takashicompany/radialex/images/04.jpg

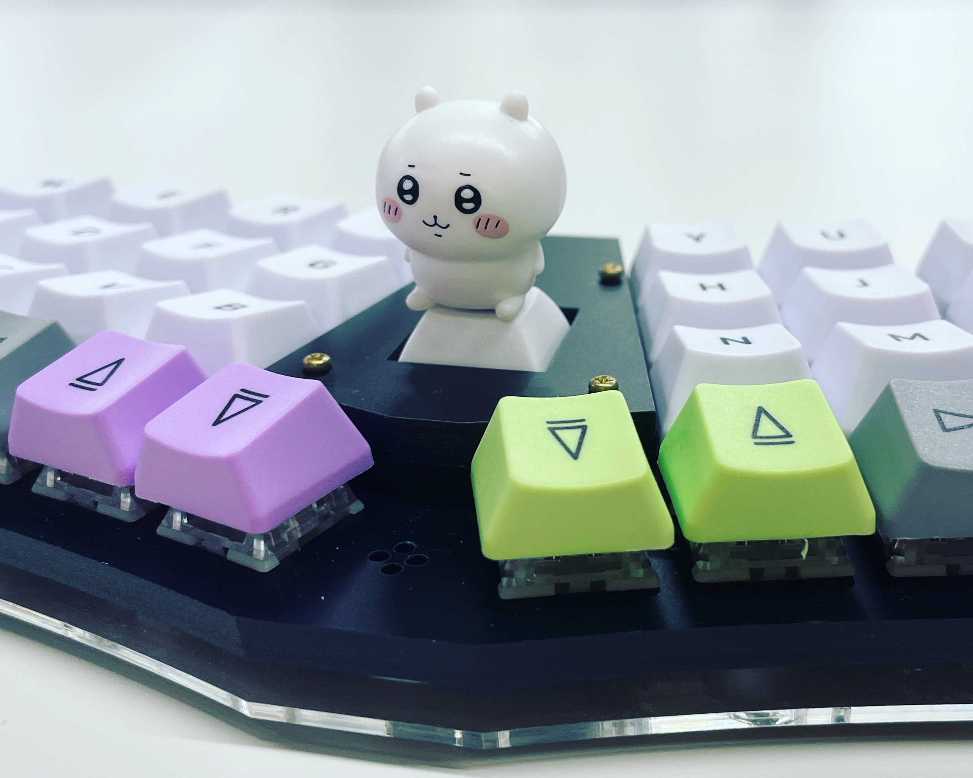
images/04.jpg
