takashicompany/radialex/images/06.jpg

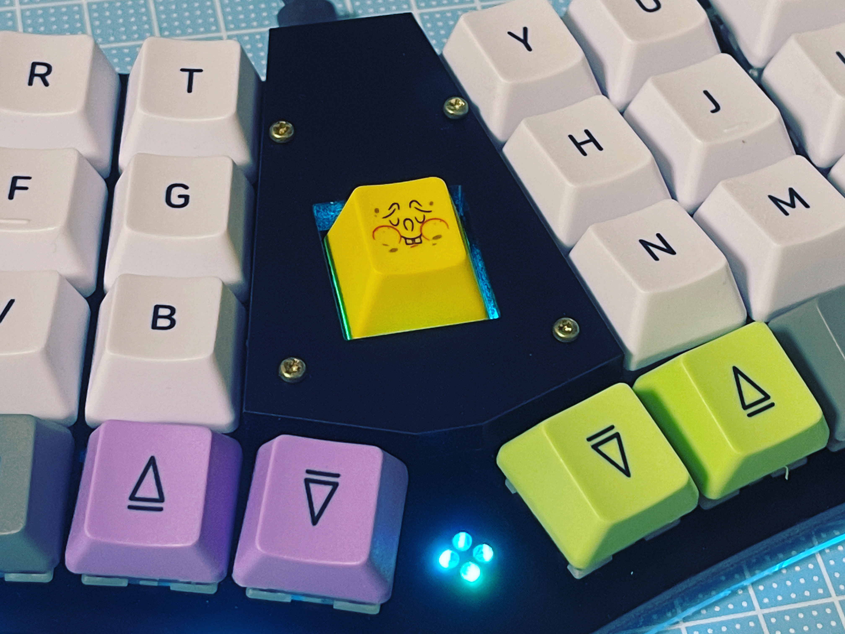
images/06.jpg
