takashicompany/radialex/images/07.jpg

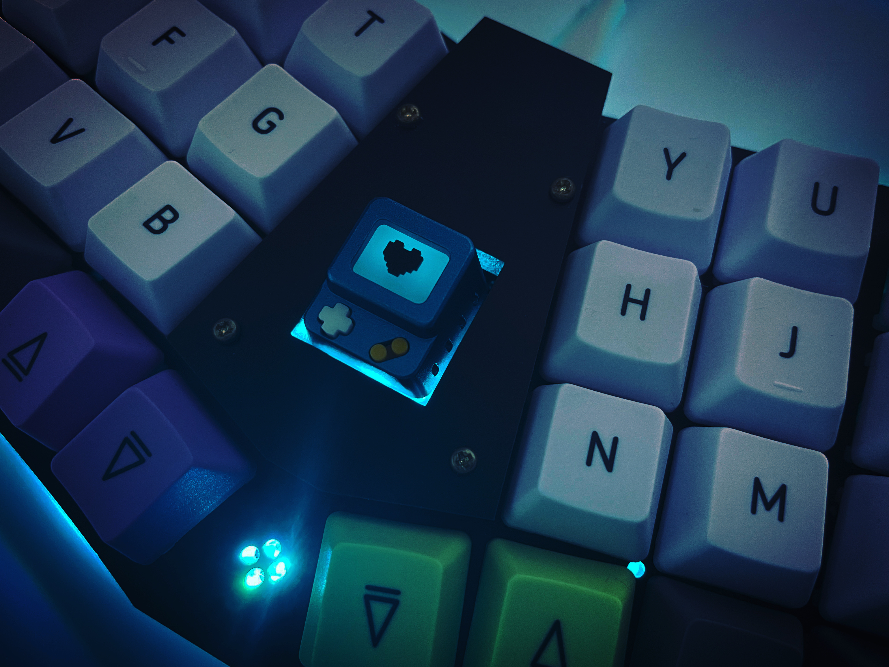
images/07.jpg
