takashicompany/radialex/images/08.jpg

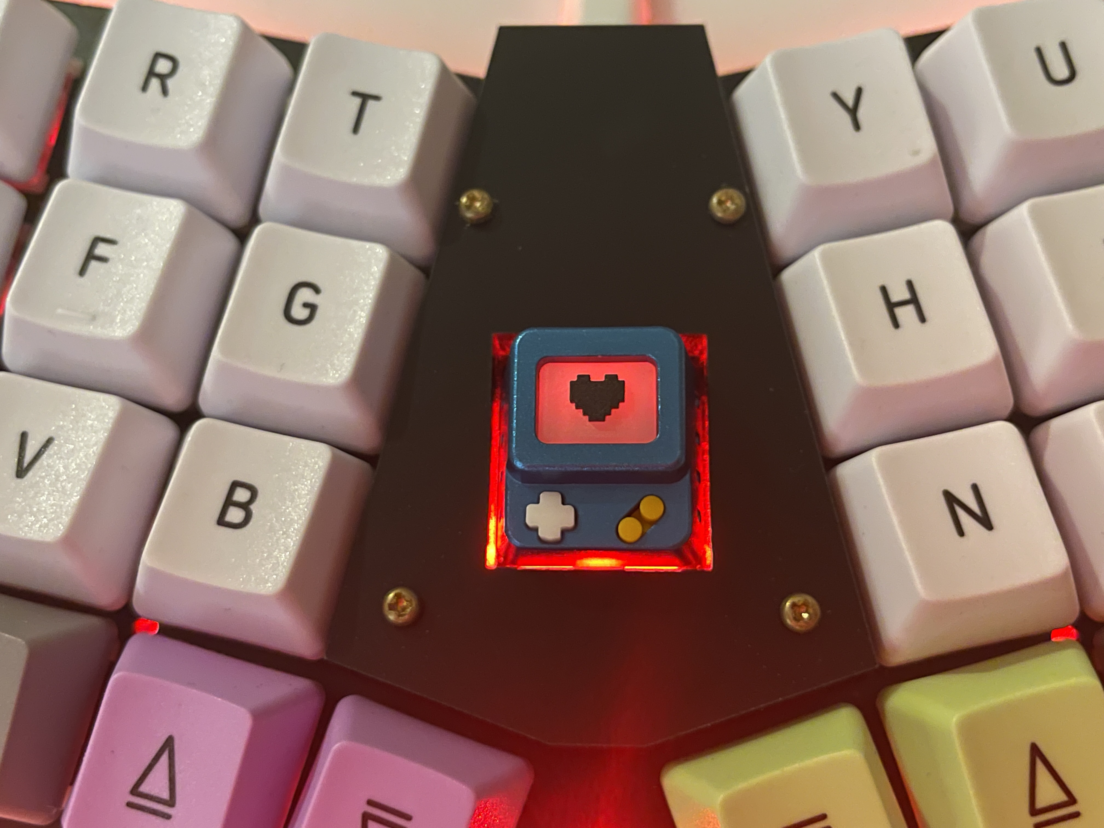
images/08.jpg
