takashicompany/radialex/images/09.jpg

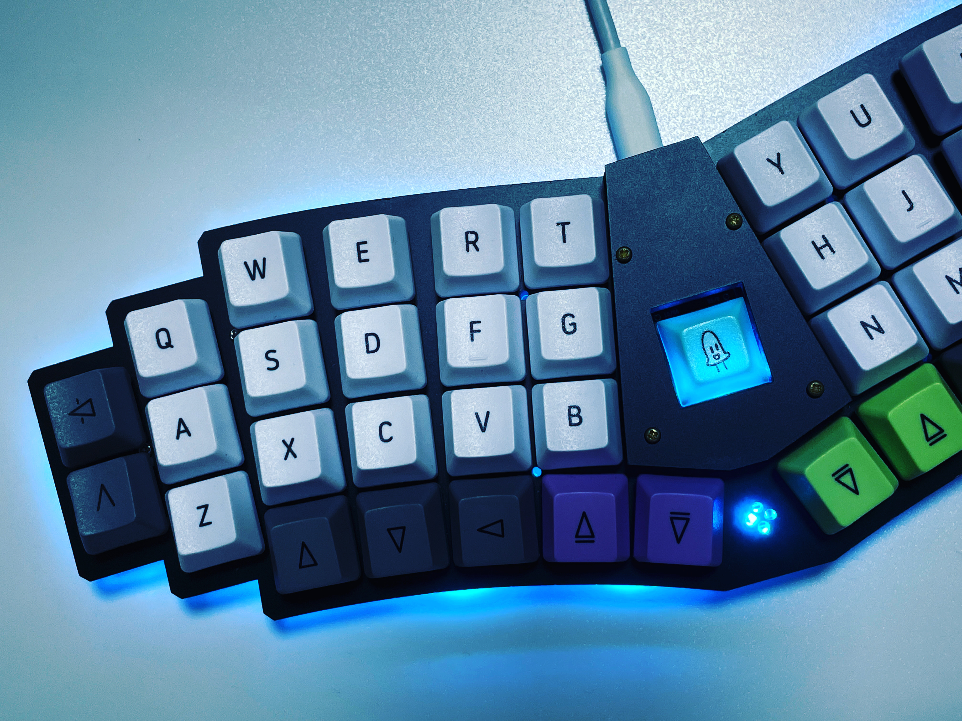
images/09.jpg
