takashicompany/radialex/images/10.jpg

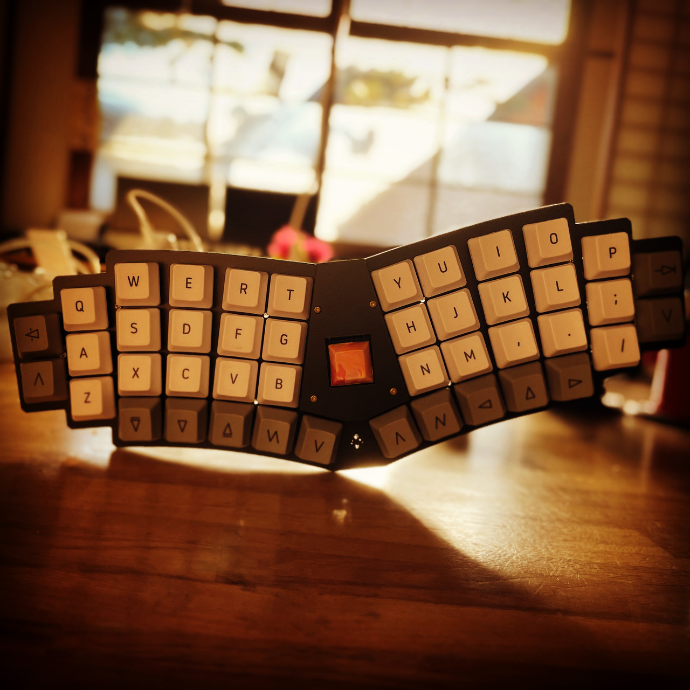
images/10.jpg
