takashicompany/radialex/images/12.jpg

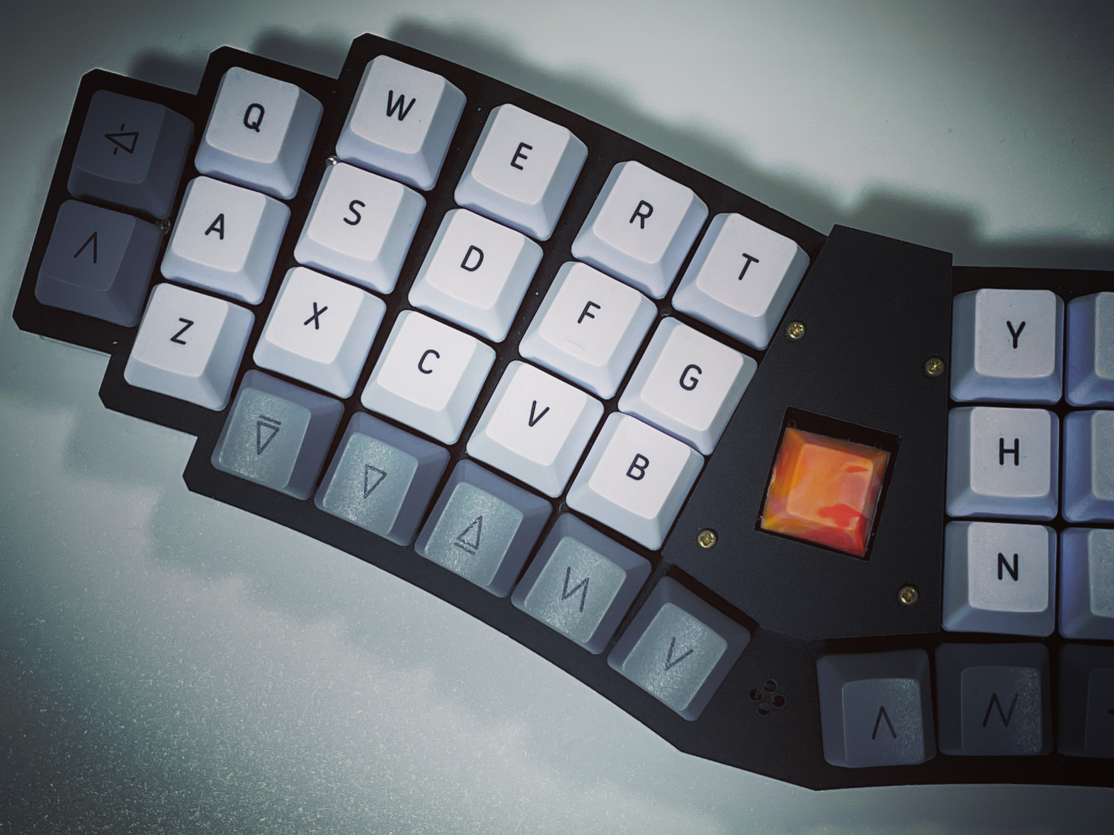
images/12.jpg
