takashicompany/radialex/images/13.jpg

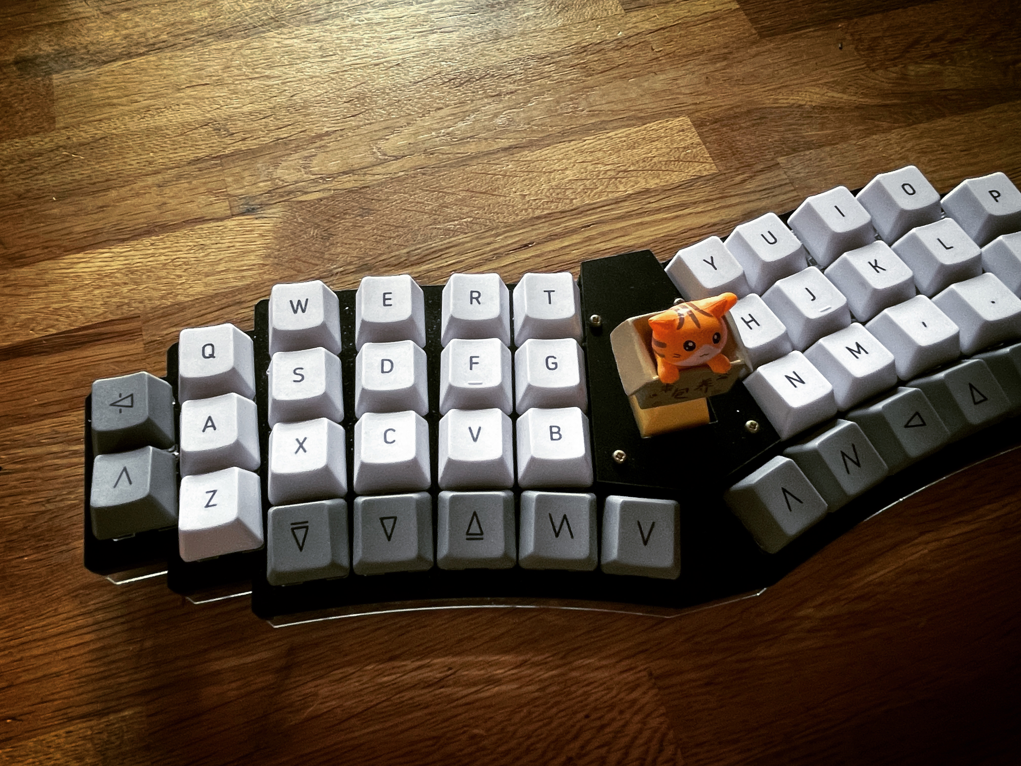
images/13.jpg
