takashicompany/radialex/images/22.jpg

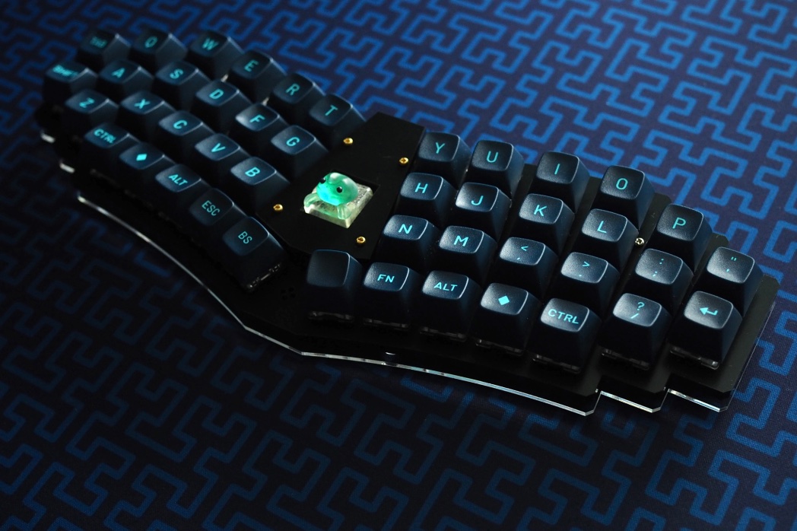
images/22.jpg
