takashicompany/radialex/images/24.jpg

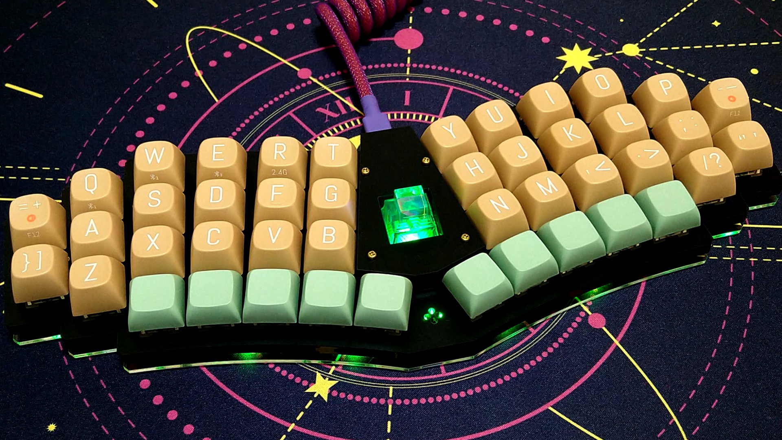
images/24.jpg
