takashicompany/radialex/images/qmk.jpg

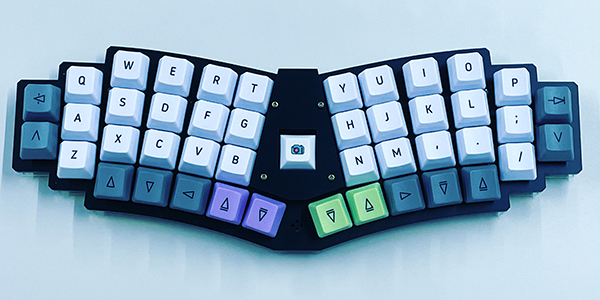
images/qmk.jpg
