takashicompany/radialex/images/build/IMG_8009.jpg

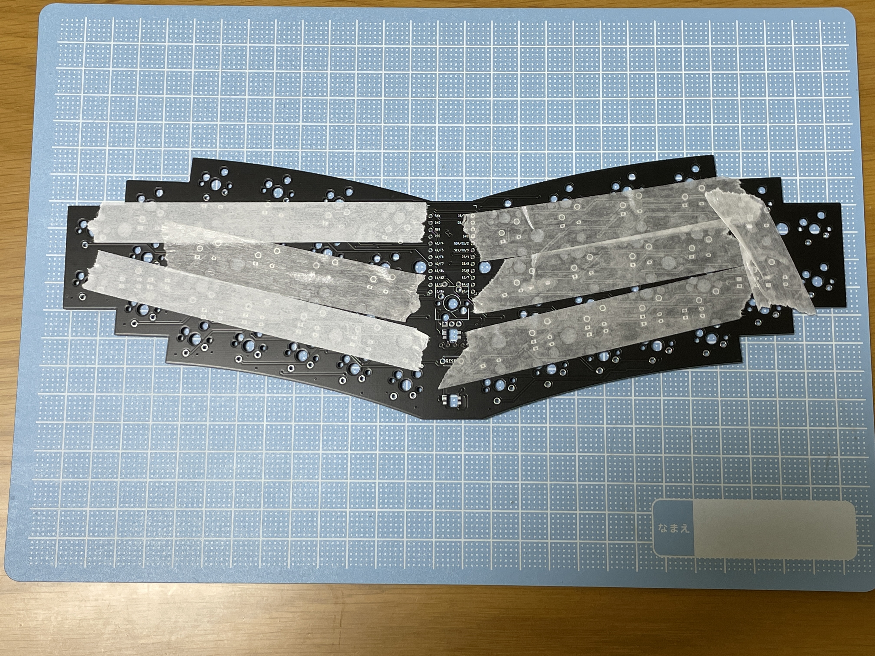
images/build/IMG_8009.jpg
