takashicompany/radialex/images/build/IMG_8306.jpg

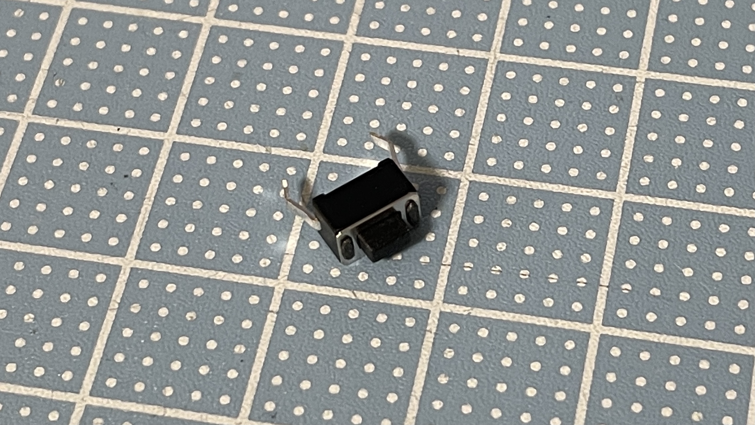
images/build/IMG_8306.jpg
