takashicompany/radialex/images/build/IMG_8320.jpg

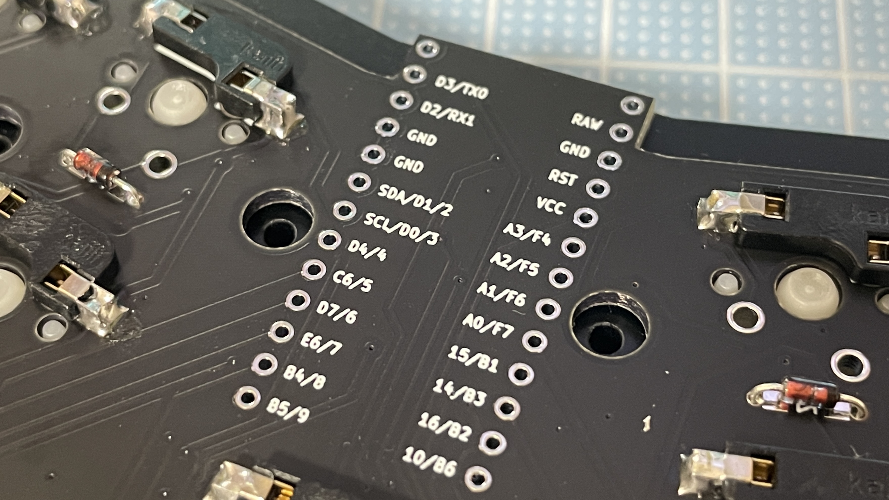
images/build/IMG_8320.jpg
