takashicompany/radialex/images/build/IMG_8321.jpg

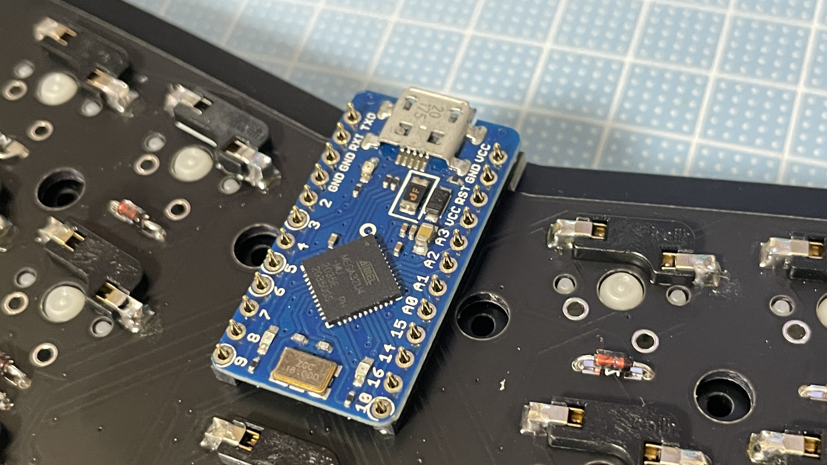
images/build/IMG_8321.jpg
