takashicompany/radialex/images/build/IMG_8509.jpg

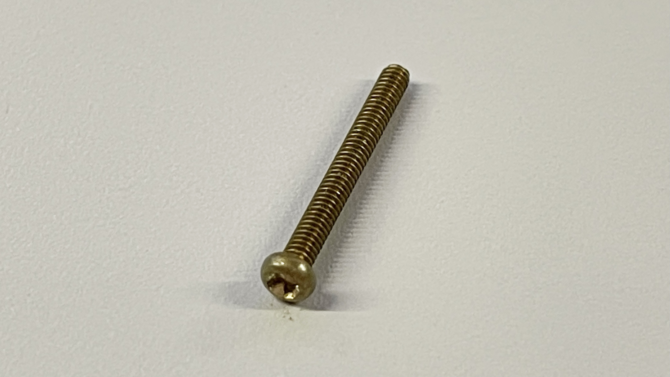
images/build/IMG_8509.jpg
