takashicompany/radialex/images/build/IMG_8510.jpg

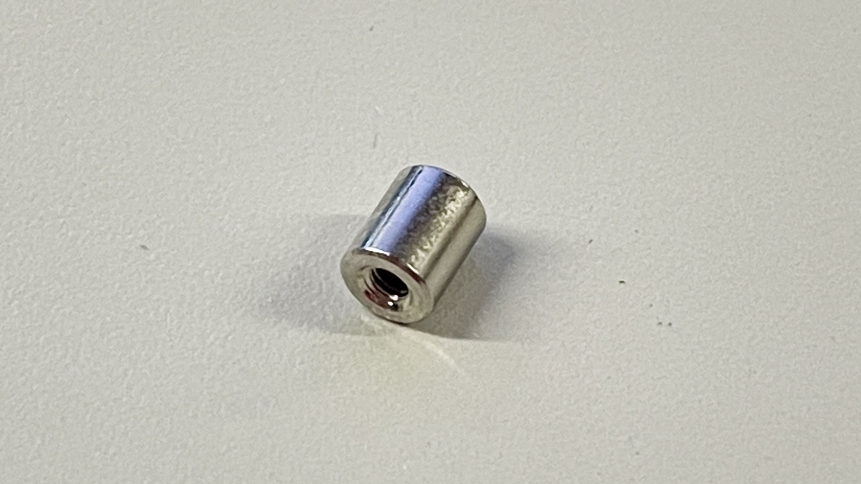
images/build/IMG_8510.jpg
