takashicompany/radialex/images/build/IMG_8511.jpg

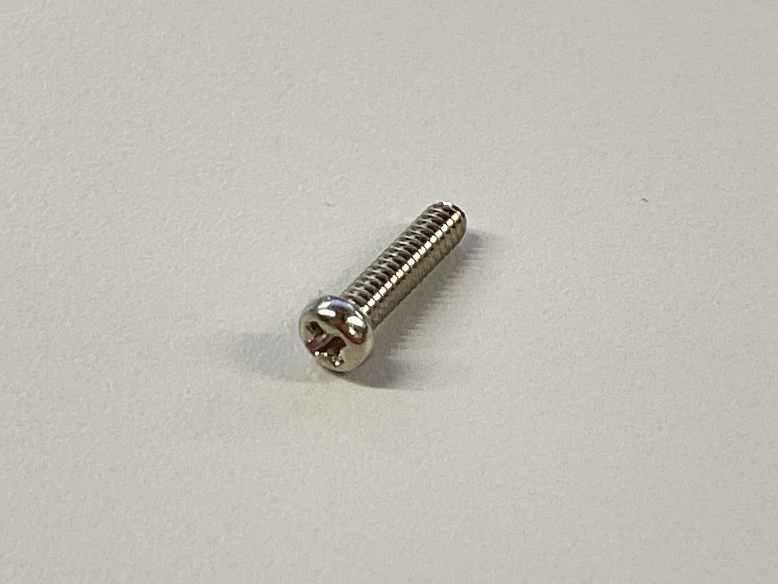
images/build/IMG_8511.jpg
