takashicompany/radialex/images/build/IMG_8513.jpg

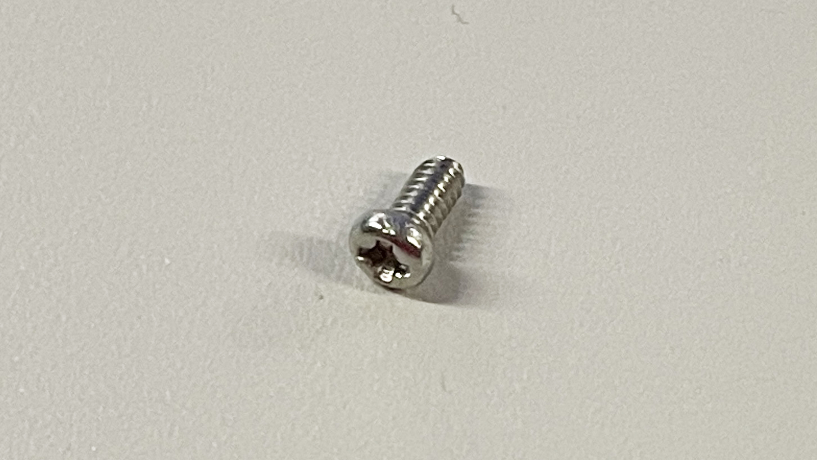
images/build/IMG_8513.jpg
