takashicompany/radialex/images/build/IMG_8516.jpg

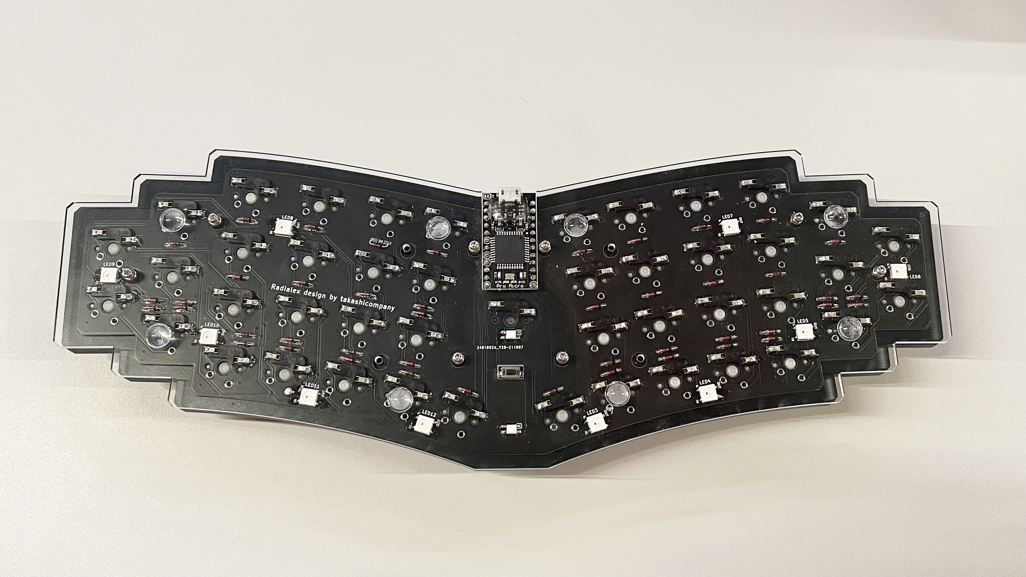
images/build/IMG_8516.jpg
