takashicompany/radialex/images/build/IMG_8812.jpg

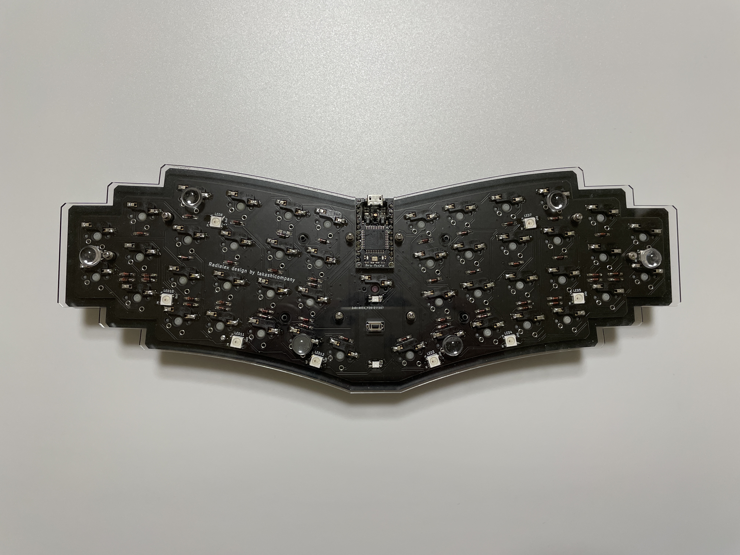
images/build/IMG_8812.jpg
