takashicompany/radialex/images/build/IMG_8814.jpg

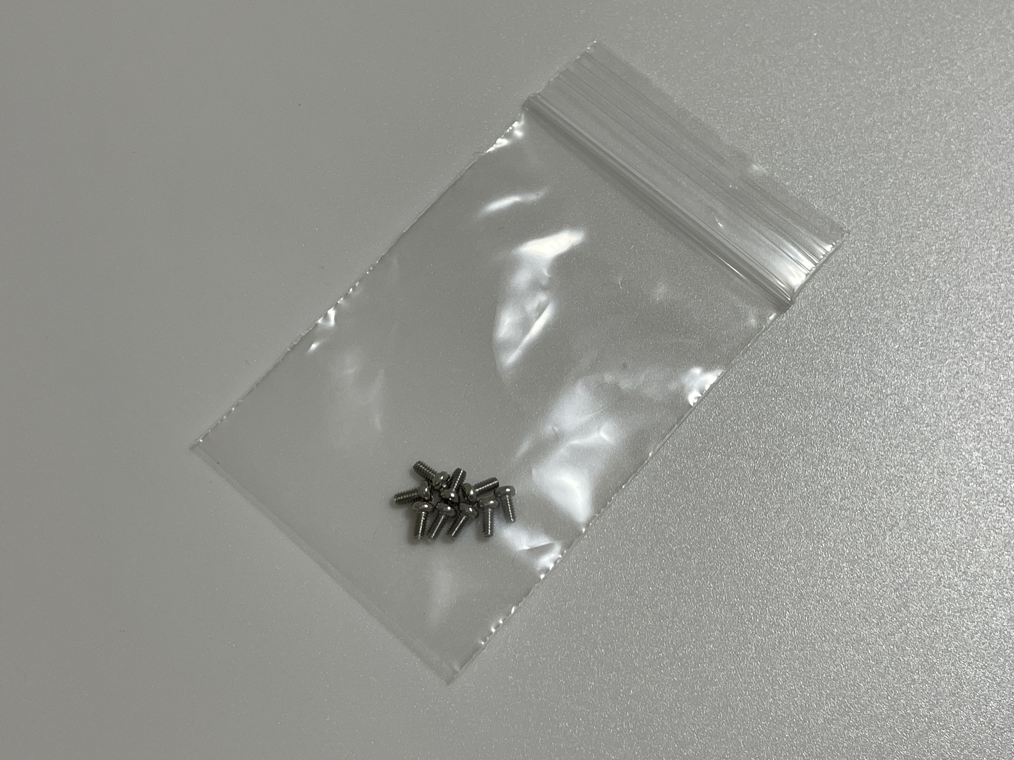
images/build/IMG_8814.jpg
