takashicompany/radialex/images/build/IMG_8815.jpg

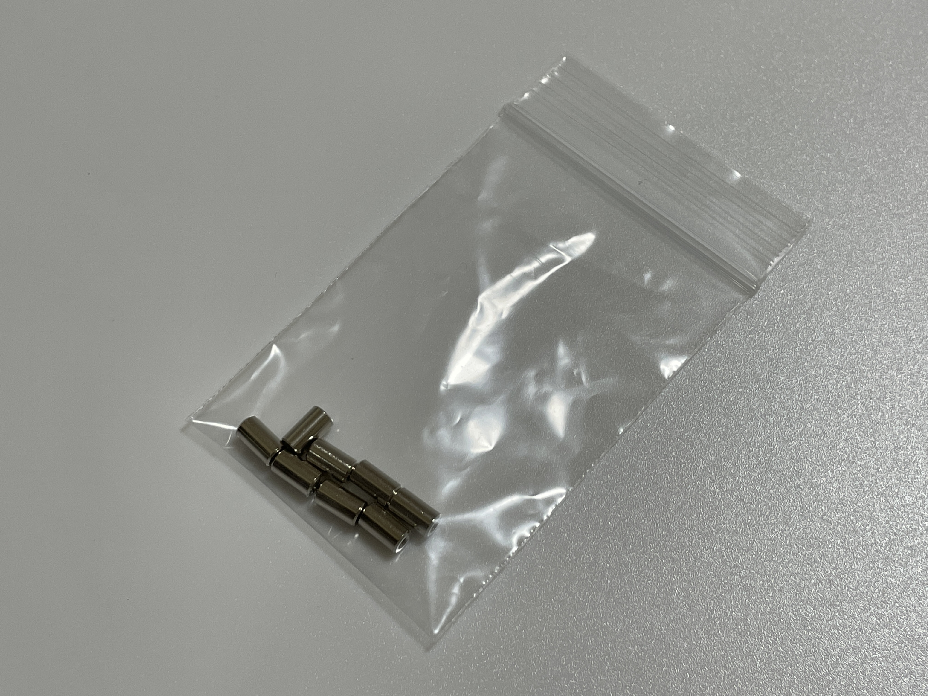
images/build/IMG_8815.jpg
