takashicompany/radialex/images/build/IMG_8816.jpg

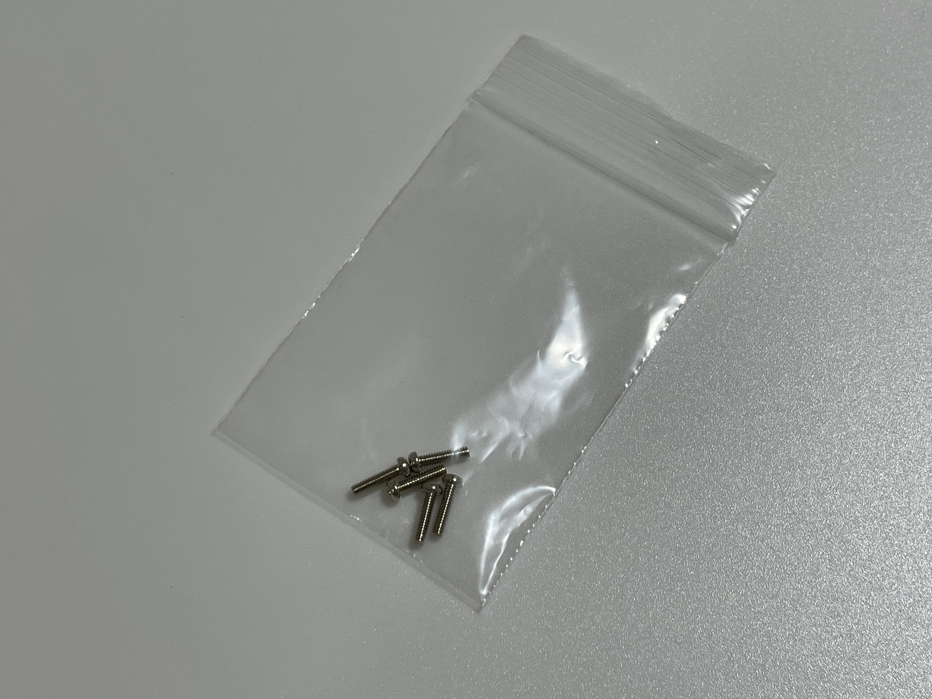
images/build/IMG_8816.jpg
