takashicompany/radialex/images/build/IMG_8817.jpg

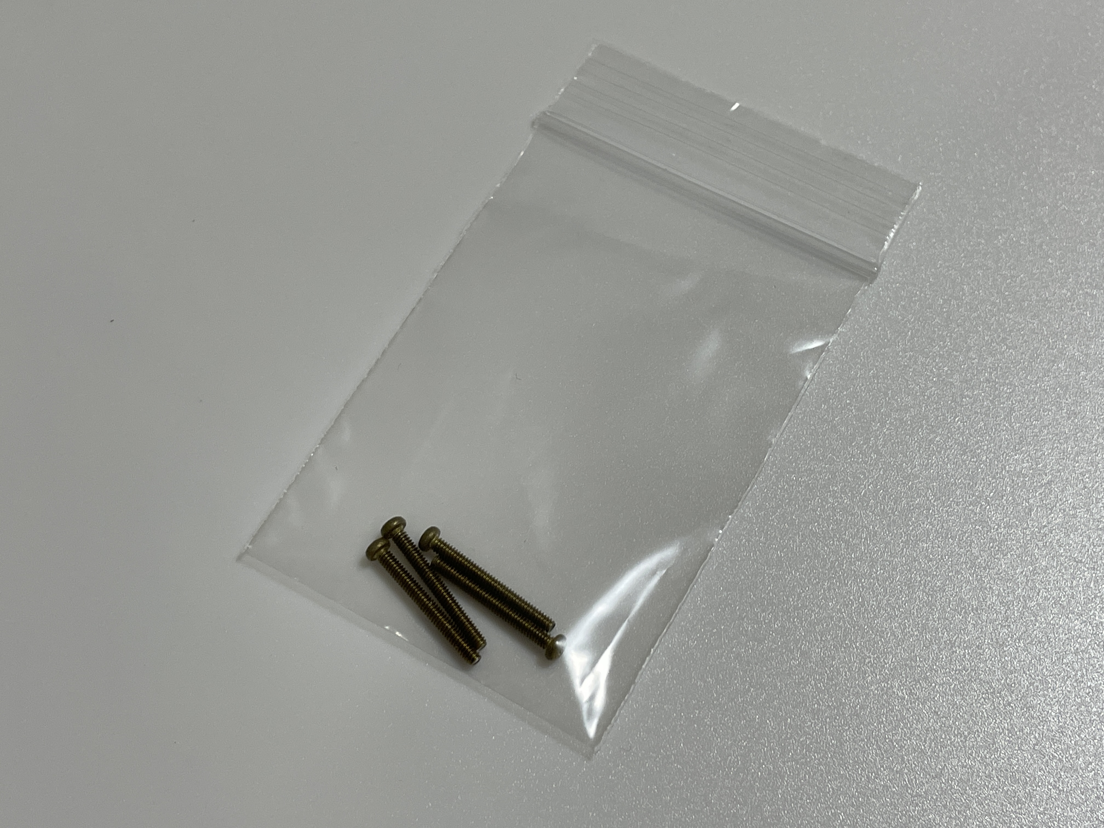
images/build/IMG_8817.jpg
