takashicompany/radialex/images/build/IMG_9180.jpg

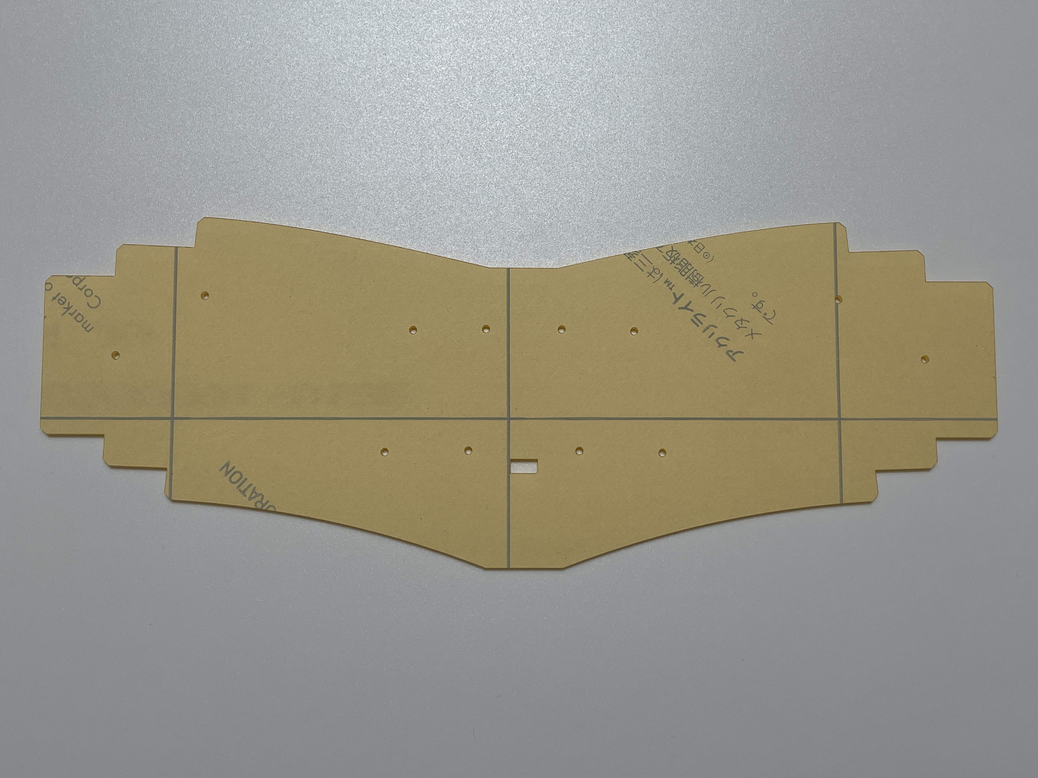
images/build/IMG_9180.jpg
