takashicompany/radialex/images/build/IMG_9181.jpg

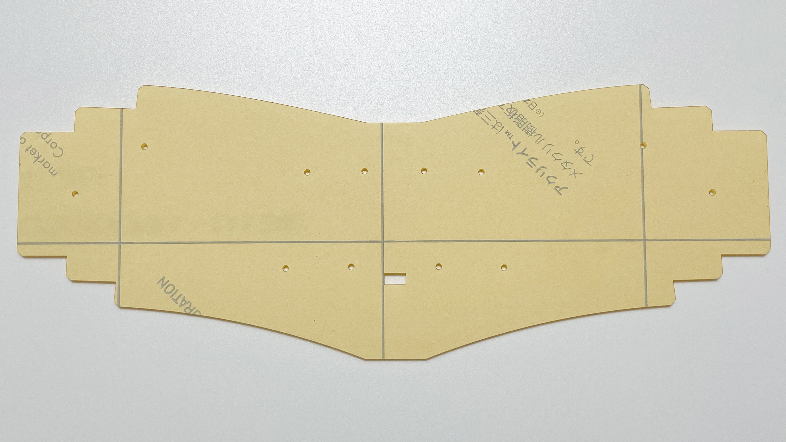
images/build/IMG_9181.jpg
