takashicompany/radialex/images/build/IMG_9183.jpg

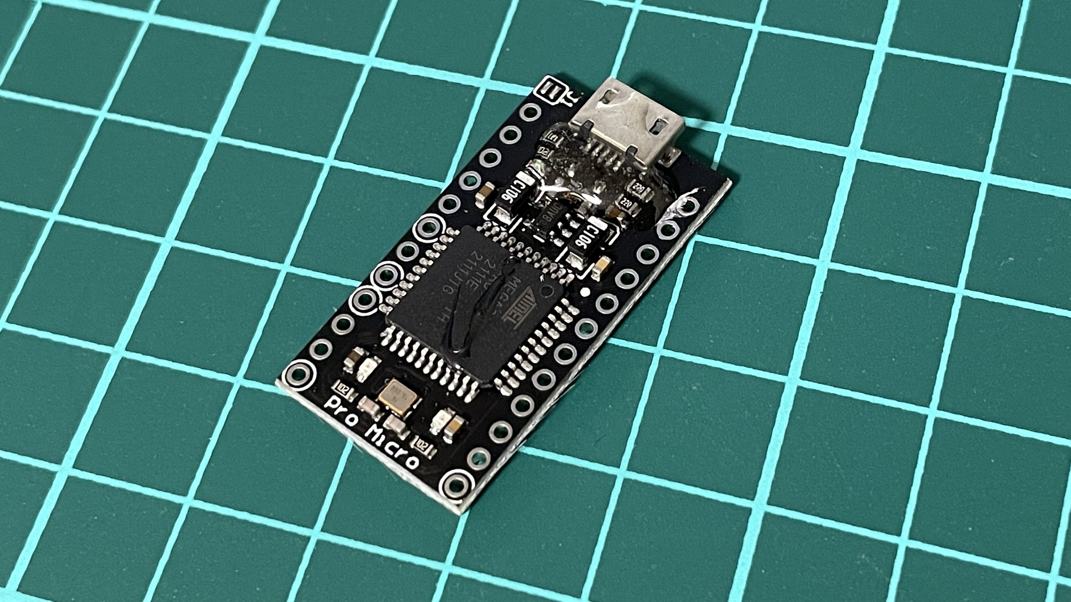
images/build/IMG_9183.jpg
