takashicompany/radialex/images/build/IMG_9199.jpg

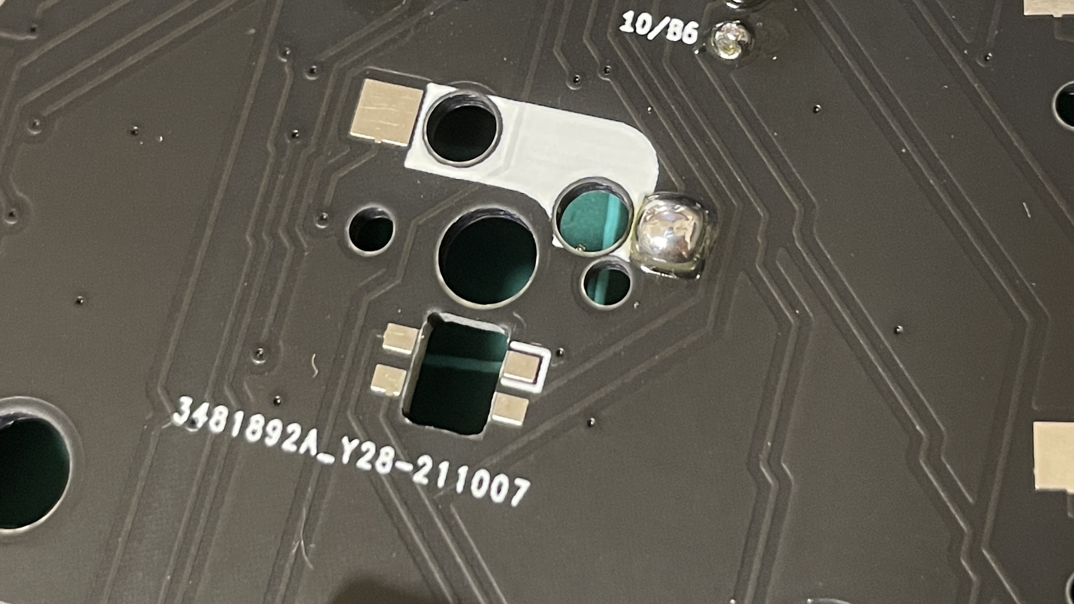
images/build/IMG_9199.jpg
