takashicompany/radialex/images/build/IMG_9201.jpg

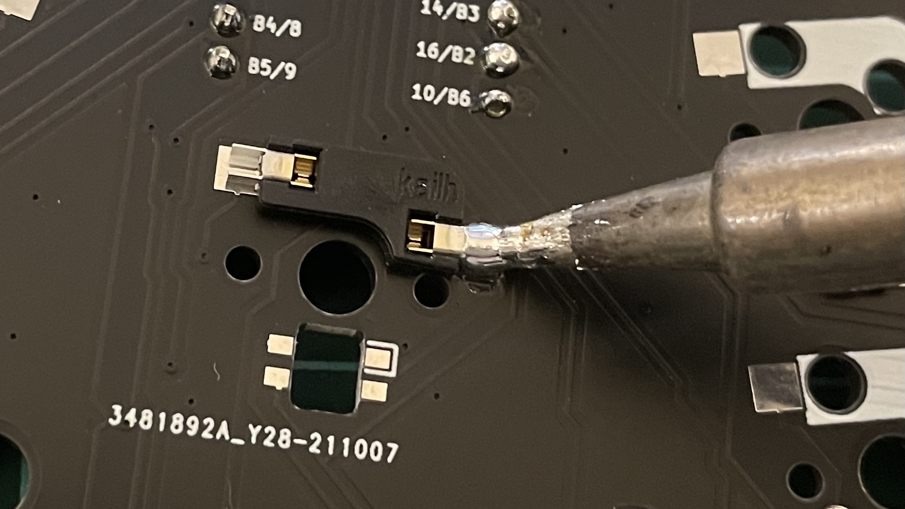
images/build/IMG_9201.jpg
