takashicompany/radialex/images/build/IMG_9202.jpg

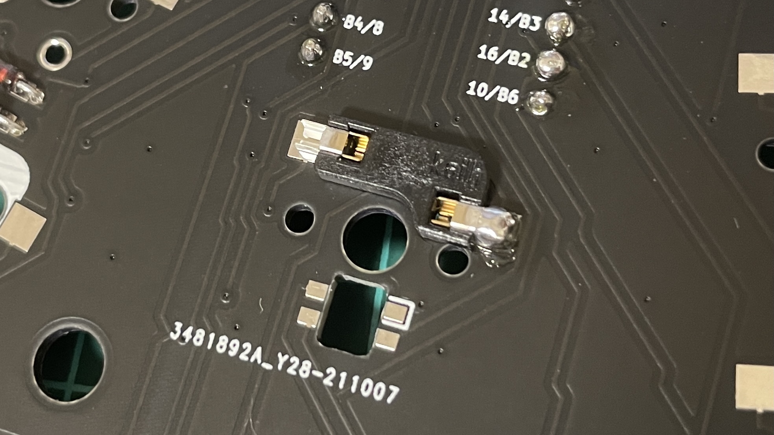
images/build/IMG_9202.jpg
