takashicompany/radialex/images/build/IMG_9203.jpg

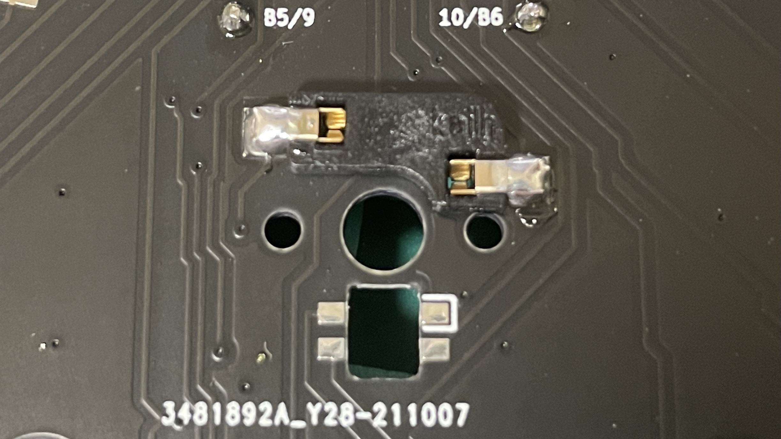
images/build/IMG_9203.jpg
