takashicompany/radialex/images/build/IMG_9205.jpg

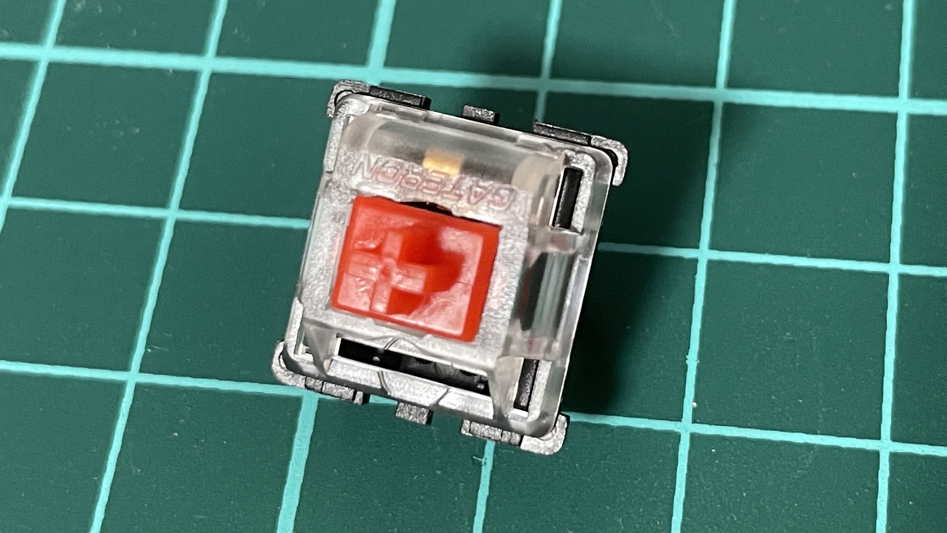
images/build/IMG_9205.jpg
