takashicompany/radialex/images/build/IMG_9207.jpg

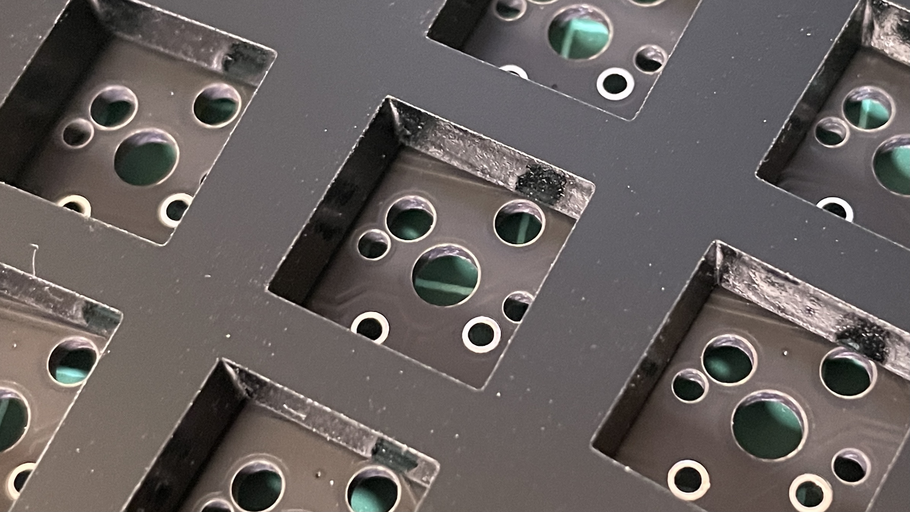
images/build/IMG_9207.jpg
