takashicompany/radialex/images/build/IMG_9211.jpg

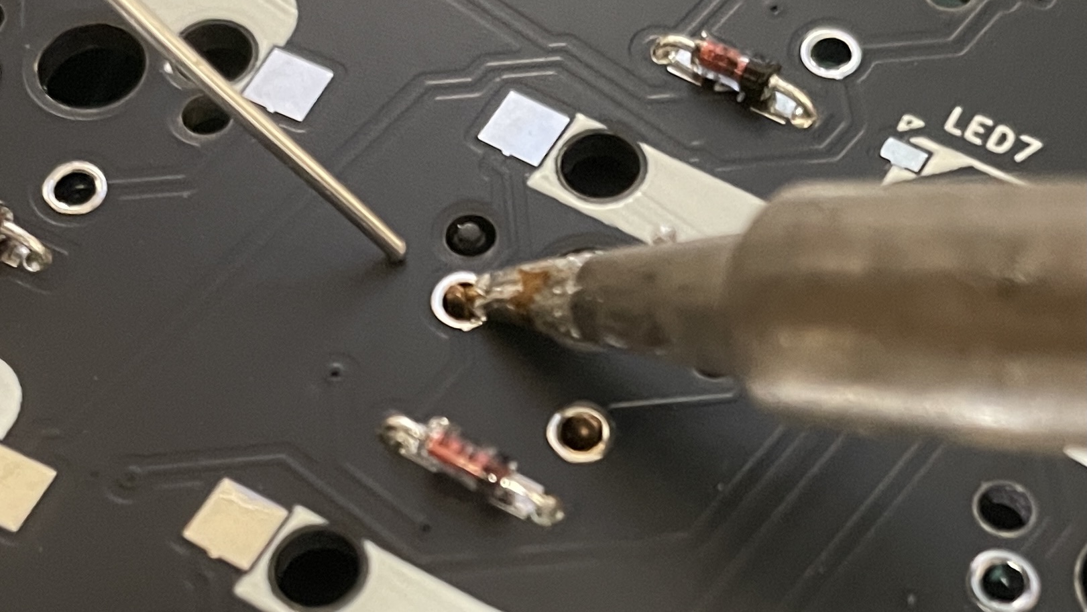
images/build/IMG_9211.jpg
