takashicompany/radialex/images/build/IMG_9213.jpg

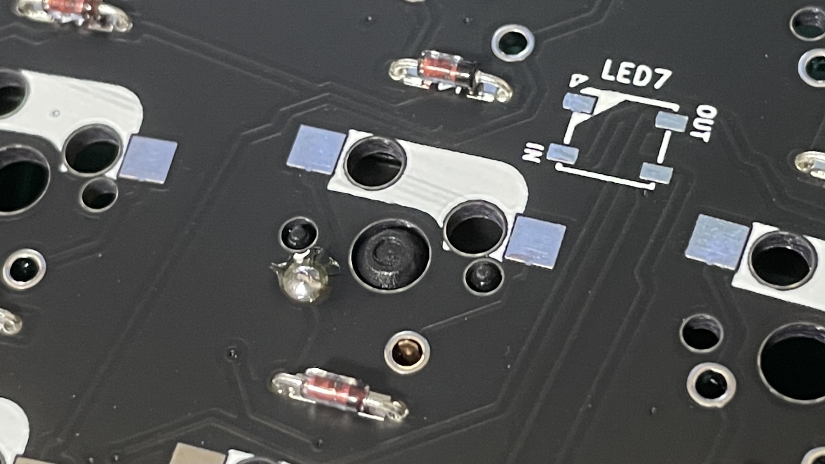
images/build/IMG_9213.jpg
