takashicompany/radialex/images/build/IMG_9214.jpg

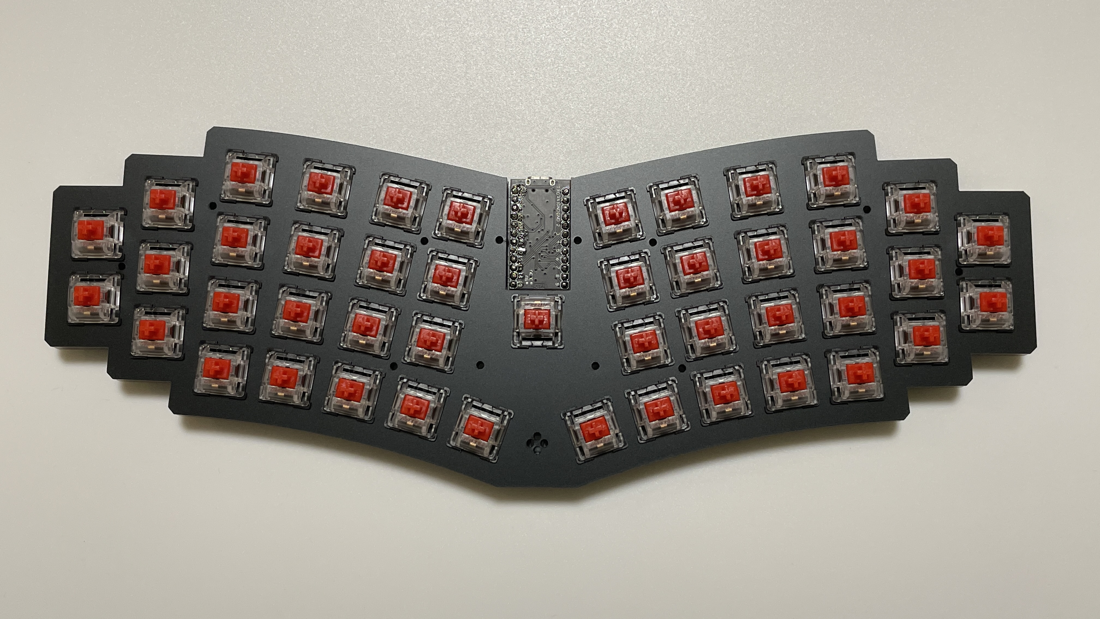
images/build/IMG_9214.jpg
