takashicompany/radialex/images/build/IMG_9217.jpg

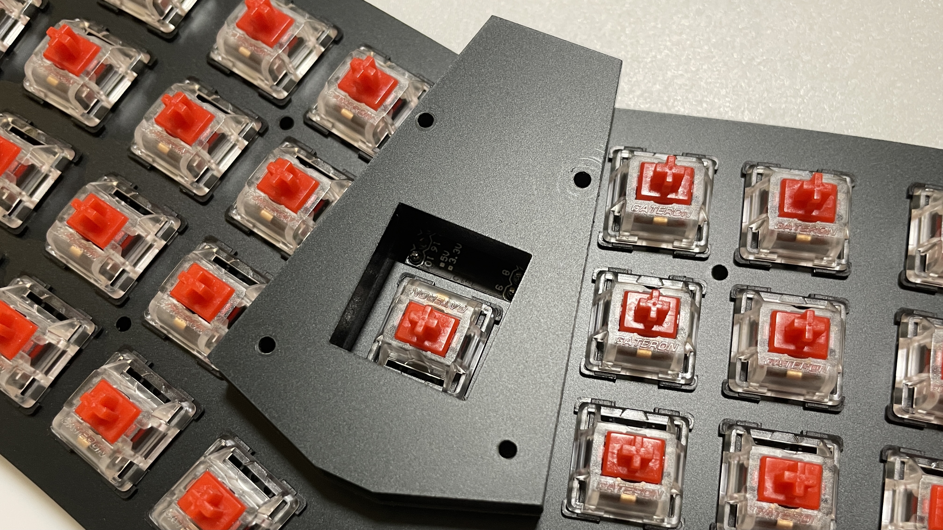
images/build/IMG_9217.jpg
